WelsTheory/Repositorio-de-Tesis/Demo SAQD_ECG/Tesis_Simulink.X/Tesis_Simulink_data.c

/*
 * -------------------------------------------------------------------
 * MPLAB 16-Bit Device Blocks for Simulink v3.38.
 *
 *   Product Page:  http://www.microchip.com/SimulinkBlocks
 *           Forum: http://www.microchip.com/forums/f192.aspx
 *           Wiki:  http://microchip.wikidot.com/simulink:start
 * -------------------------------------------------------------------
 * File: Tesis_Simulink_data.c
 *
 * Code generated for Simulink model 'Tesis_Simulink'.
 *
 * Model version                  : 1.143
 * Simulink Coder version         : 8.6 (R2014a) 27-Dec-2013
 * C/C++ source code generated on : Sun Jul 07 20:59:31 2019
 */

#include "Tesis_Simulink.h"
#include "Tesis_Simulink_private.h"

/* Constant parameters (auto storage) */
const ConstP_Tesis_Simulink_T Tesis_Simulink_ConstP = {
  /* Computed Parameter: Filtro_40Hz_Orden_20_Coefficients
   * Referenced by: '<S2>/Filtro_40Hz_Orden_20'
   */
  { 0.00203286763F, 0.00379420863F, 0.00820735097F, 0.0163565241F, 0.0286096856F,
    0.0444048606F, 0.0622486696F, 0.0799414217F, 0.0949862376F, 0.105091862F,
    0.108652636F, 0.105091862F, 0.0949862376F, 0.0799414217F, 0.0622486696F,
    0.0444048606F, 0.0286096856F, 0.0163565241F, 0.00820735097F, 0.00379420863F,
    0.00203286763F },

  /* Computed Parameter: Filtro_05Hz_Orden_2_Coefficients
   * Referenced by: '<S2>/Filtro_05Hz_Orden_2'
   */
  { -7.99903137E-5F, -0.00016783434F, -0.000397814467F, -0.000682088779F,
    -0.000912073359F, 0.998920083F, -0.000912073359F, -0.000682088779F,
    -0.000397814467F, -0.00016783434F, -7.99903137E-5F },

  /* Computed Parameter: Filtro_40Hz_Orden_5_Coefficients
   * Referenced by: '<S2>/Filtro_40Hz_Orden_5'
   */
  { 0.0272522252F, 0.141468123F, 0.331279665F, 0.331279665F, 0.141468123F,
    0.0272522252F },

  /* Computed Parameter: Filtro_40Hz_Orden_15_Coefficients
   * Referenced by: '<S2>/Filtro_40Hz_Orden_15'
   */
  { 0.00543942489F, 0.00986033119F, 0.022235956F, 0.0428936221F, 0.0694174543F,
    0.0970705152F, 0.120029137F, 0.133053556F, 0.133053556F, 0.120029137F,
    0.0970705152F, 0.0694174543F, 0.0428936221F, 0.022235956F, 0.00986033119F,
    0.00543942489F },

  /* Computed Parameter: Filtro_40Hz_Orden_30_Coefficients
   * Referenced by: '<S2>/Filtro_40Hz_Orden_30'
   */
  { -0.00108586519F, -0.000820198795F, -0.000399968849F, 0.000607254158F,
    0.00269167544F, 0.00631159171F, 0.011798257F, 0.0192719586F, 0.0285849664F,
    0.0393032022F, 0.0507324189F, 0.0619873591F, 0.072095111F, 0.080117844F,
    0.0852764249F, 0.0870559365F, 0.0852764249F, 0.080117844F, 0.072095111F,
    0.0619873591F, 0.0507324189F, 0.0393032022F, 0.0285849664F, 0.0192719586F,
    0.011798257F, 0.00631159171F, 0.00269167544F, 0.000607254158F,
    -0.000399968849F, -0.000820198795F, -0.00108586519F }
};

/*
 * File trailer for generated code.
 *
 * [EOF]
 */
