WelsTheory/Repositorio-de-Tesis/Demo SAQD_ECG/Tesis_Simulink.X/rt_nonfinite.c

/*
 * -------------------------------------------------------------------
 * MPLAB 16-Bit Device Blocks for Simulink v3.38.
 *
 *   Product Page:  http://www.microchip.com/SimulinkBlocks
 *           Forum: http://www.microchip.com/forums/f192.aspx
 *           Wiki:  http://microchip.wikidot.com/simulink:start
 * -------------------------------------------------------------------
 * File: rt_nonfinite.c
 *
 * Code generated for Simulink model 'Tesis_Simulink'.
 *
 * Model version                  : 1.143
 * Simulink Coder version         : 8.6 (R2014a) 27-Dec-2013
 * C/C++ source code generated on : Sun Jul 07 20:59:31 2019
 */

/*
 * Abstract:
 *      Function to intialize non-finites,
 *      (Inf, NaN and -Inf).
 */
#include "rt_nonfinite.h"
#include "rtGetNaN.h"
#include "rtGetInf.h"

real_T rtInf;
real_T rtMinusInf;
real_T rtNaN;
real32_T rtInfF;
real32_T rtMinusInfF;
real32_T rtNaNF;

/*
 * Initialize the rtInf, rtMinusInf, and rtNaN needed by the
 * generated code. NaN is initialized as non-signaling. Assumes IEEE.
 */
void rt_InitInfAndNaN(size_t realSize)
{
  (void) (realSize);
  rtNaN = rtGetNaN();
  rtNaNF = rtGetNaNF();
  rtInf = rtGetInf();
  rtInfF = rtGetInfF();
  rtMinusInf = rtGetMinusInf();
  rtMinusInfF = rtGetMinusInfF();
}

/* Test if value is infinite */
boolean_T rtIsInf(real_T value)
{
  return (boolean_T)((value==rtInf || value==rtMinusInf) ? 1U : 0U);
}

/* Test if single-precision value is infinite */
boolean_T rtIsInfF(real32_T value)
{
  return (boolean_T)(((value)==rtInfF || (value)==rtMinusInfF) ? 1U : 0U);
}

/* Test if value is not a number */
boolean_T rtIsNaN(real_T value)
{
  return (boolean_T)((value!=value) ? 1U : 0U);
}

/* Test if single-precision value is not a number */
boolean_T rtIsNaNF(real32_T value)
{
  return (boolean_T)(((value!=value) ? 1U : 0U));
}

/*
 * File trailer for generated code.
 *
 * [EOF]
 */
