WelsTheory/Repositorio-de-Tesis/Framework/Ejemplo_de_Programa_principal.X/MCHP_modelInclude.h

/******************************************************/
/* This file includes simulink model public .h files. */
/* File name will not depends on model's name 	      */
/* simplifying inclusion for your shared c/h added    */
/* code (if any)  	                                  */
/******************************************************/

#include "Ejemplo_de_Programa_principal.h"
#include "Ejemplo_de_Programa_principal_private.h"
