WelsTheory/Repositorio-de-Tesis/Carpeta de Pruebas/Prueba_ADC.X/Prueba_ADC_data.c

/*
 * -------------------------------------------------------------------
 * MPLAB 16-Bit Device Blocks for Simulink v3.38.
 *
 *   Product Page:  http://www.microchip.com/SimulinkBlocks
 *           Forum: http://www.microchip.com/forums/f192.aspx
 *           Wiki:  http://microchip.wikidot.com/simulink:start
 * -------------------------------------------------------------------
 * File: Prueba_ADC_data.c
 *
 * Code generated for Simulink model 'Prueba_ADC'.
 *
 * Model version                  : 1.43
 * Simulink Coder version         : 8.6 (R2014a) 27-Dec-2013
 * C/C++ source code generated on : Mon Feb 18 00:49:58 2019
 */

#include "Prueba_ADC.h"
#include "Prueba_ADC_private.h"

/* Constant parameters (auto storage) */
const ConstP_Prueba_ADC_T Prueba_ADC_ConstP = {
  /* Computed Parameter: Filter_0540_HP_1_Coefficients
   * Referenced by: '<Root>/Filter_0540_HP_1'
   */
  { -0.000722855737F, -0.00317084719F, -0.00576246856F, -0.00834118761F,
    -0.0107321292F, -0.0127506247F, -0.0142119713F, -0.01494186F, -0.0147868991F,
    -0.0136246076F, -0.0113722663F, -0.00799405482F, -0.00350597757F,
    0.00202179234F, 0.00846539345F, 0.0156506654F, 0.0233593453F, 0.0313378349F,
    0.0393081084F, 0.0469802357F, 0.0540658571F, 0.0602918938F, 0.0654137582F,
    0.0692273453F, 0.071579136F, 0.0723738372F, 0.071579136F, 0.0692273453F,
    0.0654137582F, 0.0602918938F, 0.0540658571F, 0.0469802357F, 0.0393081084F,
    0.0313378349F, 0.0233593453F, 0.0156506654F, 0.00846539345F, 0.00202179234F,
    -0.00350597757F, -0.00799405482F, -0.0113722663F, -0.0136246076F,
    -0.0147868991F, -0.01494186F, -0.0142119713F, -0.0127506247F, -0.0107321292F,
    -0.00834118761F, -0.00576246856F, -0.00317084719F, -0.000722855737F },

  /* Computed Parameter: Filter_40_HP_50_Coefficients
   * Referenced by: '<Root>/Filter_40_HP_50'
   */
  { -2.66366964E-18F, -0.00287274597F, -0.00591556495F, -0.00894370489F,
    -0.0117507577F, -0.0141187599F, -0.0158297028F, -0.0166778471F,
    -0.0164821465F, -0.0150980344F, -0.012427886F, -0.00842943F, -0.00312157185F,
    0.00341284438F, 0.0110276015F, 0.0195171088F, 0.0286237169F, 0.0380480699F,
    0.0474619828F, 0.0565232038F, 0.0648913532F, 0.0722440779F, 0.0782926604F,
    0.0827961788F, 0.0855734125F, 0.0865118653F, 0.0855734125F, 0.0827961788F,
    0.0782926604F, 0.0722440779F, 0.0648913532F, 0.0565232038F, 0.0474619828F,
    0.0380480699F, 0.0286237169F, 0.0195171088F, 0.0110276015F, 0.00341284438F,
    -0.00312157185F, -0.00842943F, -0.012427886F, -0.0150980344F, -0.0164821465F,
    -0.0166778471F, -0.0158297028F, -0.0141187599F, -0.0117507577F,
    -0.00894370489F, -0.00591556495F, -0.00287274597F, -2.66366964E-18F }
};

/*
 * File trailer for generated code.
 *
 * [EOF]
 */
