WelsTheory/Repositorio-de-Tesis/Carpeta de Pruebas/DSPIC33FJ_FIR.X/DSPIC33FJ_FIR_private.h

/*
 * -------------------------------------------------------------------
 * MPLAB 16-Bit Device Blocks for Simulink v3.38.
 *
 *   Product Page:  http://www.microchip.com/SimulinkBlocks
 *           Forum: http://www.microchip.com/forums/f192.aspx
 *           Wiki:  http://microchip.wikidot.com/simulink:start
 * -------------------------------------------------------------------
 * File: DSPIC33FJ_FIR_private.h
 *
 * Code generated for Simulink model 'DSPIC33FJ_FIR'.
 *
 * Model version                  : 1.77
 * Simulink Coder version         : 8.6 (R2014a) 27-Dec-2013
 * C/C++ source code generated on : Sun Dec 09 18:39:59 2018
 */

#ifndef RTW_HEADER_DSPIC33FJ_FIR_private_h_
#define RTW_HEADER_DSPIC33FJ_FIR_private_h_
#include "rtwtypes.h"
#ifndef __RTWTYPES_H__
#error This file requires rtwtypes.h to be included
#endif                                 /* __RTWTYPES_H__ */

/* Declare UART1 Tx Circular Buffer Structure */
extern MCHP_UART1_TxStr MCHP_UART1_Tx;
extern MCHP_UART1_RxStr MCHP_UART1_Rx;

#endif                                 /* RTW_HEADER_DSPIC33FJ_FIR_private_h_ */

/*
 * File trailer for generated code.
 *
 * [EOF]
 */
