WelsTheory/Repositorio-de-Tesis/Carpeta de Pruebas/ECG_Physionet/Hola/mcode/ADC_DSPIC33.X/rtGetInf.h

/*
 * -------------------------------------------------------------------
 * MPLAB 16-Bit Device Blocks for Simulink v3.38.
 *
 *   Product Page:  http://www.microchip.com/SimulinkBlocks
 *           Forum: http://www.microchip.com/forums/f192.aspx
 *           Wiki:  http://microchip.wikidot.com/simulink:start
 * -------------------------------------------------------------------
 * File: rtGetInf.h
 *
 * Code generated for Simulink model 'ADC_DSPIC33'.
 *
 * Model version                  : 1.216
 * Simulink Coder version         : 8.6 (R2014a) 27-Dec-2013
 * C/C++ source code generated on : Tue Dec 18 17:40:23 2018
 */

#ifndef RTW_HEADER_rtGetInf_h_
#define RTW_HEADER_rtGetInf_h_
#include <stddef.h>
#include "rtwtypes.h"
#include "rt_nonfinite.h"

extern real_T rtGetInf(void);
extern real32_T rtGetInfF(void);
extern real_T rtGetMinusInf(void);
extern real32_T rtGetMinusInfF(void);

#endif                                 /* RTW_HEADER_rtGetInf_h_ */

/*
 * File trailer for generated code.
 *
 * [EOF]
 */
