WelsTheory/Repositorio-de-Tesis/Carpeta de Pruebas/ECG_Physionet/Hola/mcode/Programa_DSPIC.X/rtmodel.h

/*
 * -------------------------------------------------------------------
 * MPLAB 16-Bit Device Blocks for Simulink v3.38.
 *
 *   Product Page:  http://www.microchip.com/SimulinkBlocks
 *           Forum: http://www.microchip.com/forums/f192.aspx
 *           Wiki:  http://microchip.wikidot.com/simulink:start
 * -------------------------------------------------------------------
 * File: rtmodel.h
 *
 * Code generated for Simulink model 'Programa_DSPIC'.
 *
 * Model version                  : 1.9
 * Simulink Coder version         : 8.6 (R2014a) 27-Dec-2013
 * C/C++ source code generated on : Thu Dec 20 15:43:44 2018
 */

#ifndef RTW_HEADER_rtmodel_h_
#define RTW_HEADER_rtmodel_h_
#include "Programa_DSPIC.h"

/* Macros generated for backwards compatibility  */
#ifndef rtmGetErrorStatus
# define rtmGetErrorStatus(rtm)        (NULL)
#endif

#ifndef rtmSetErrorStatus
# define rtmSetErrorStatus(rtm, val)   (NULL)
#endif
#endif                                 /* RTW_HEADER_rtmodel_h_ */

/*
 * File trailer for generated code.
 *
 * [EOF]
 */
