WelsTheory/Repositorio-de-Tesis/Carpeta de Pruebas/hola_dspic.X/hola_dspic_data.c

/*
 * -------------------------------------------------------------------
 * MPLAB 16-Bit Device Blocks for Simulink v3.38.
 *
 *   Product Page:  http://www.microchip.com/SimulinkBlocks
 *           Forum: http://www.microchip.com/forums/f192.aspx
 *           Wiki:  http://microchip.wikidot.com/simulink:start
 * -------------------------------------------------------------------
 * File: hola_dspic_data.c
 *
 * Code generated for Simulink model 'hola_dspic'.
 *
 * Model version                  : 1.124
 * Simulink Coder version         : 8.12 (R2017a) 16-Feb-2017
 * C/C++ source code generated on : Sun Nov 11 19:55:10 2018
 */

#include "hola_dspic.h"
#include "hola_dspic_private.h"

/* Constant parameters (auto storage) */
const ConstP_hola_dspic_T hola_dspic_ConstP = {
  /* Computed Parameter: FIR100_Coefficients
   * Referenced by: '<Root>/FIR100'
   */
  { -2.93238E-18F, -0.00152284489F, -0.00301876059F, -0.00439115381F,
    -0.00554666575F, -0.00640110951F, -0.00688511226F, -0.00694910809F,
    -0.00656735152F, -0.00574067235F, -0.00449775F, -0.00289477361F,
    -0.00101342739F, 0.00104274449F, 0.00315345684F, 0.00518805347F,
    0.00701281102F, 0.00849880371F, 0.00952989142F, 0.010010398F, 0.00987201F,
    0.00907949172F, 0.00763483858F, 0.00557956519F, 0.00299493037F,
    -3.07145458E-18F, -0.00325244456F, -0.00658200914F, -0.00978855882F,
    -0.0126615046F, -0.0149900736F, -0.0165740475F, -0.0172344446F, -0.01682356F,
    -0.0152338631F, -0.0124052288F, -0.00833010115F, -0.00305626774F,
    0.00331296818F, 0.0106212832F, 0.018664442F, 0.0271978304F, 0.0359460711F,
    0.0446143337F, 0.0529007502F, 0.0605094396F, 0.0671634153F, 0.0726168528F,
    0.0766660422F, 0.0791585296F, 0.08F, 0.0791585296F, 0.0766660422F,
    0.0726168528F, 0.0671634153F, 0.0605094396F, 0.0529007502F, 0.0446143337F,
    0.0359460711F, 0.0271978304F, 0.018664442F, 0.0106212832F, 0.00331296818F,
    -0.00305626774F, -0.00833010115F, -0.0124052288F, -0.0152338631F,
    -0.01682356F, -0.0172344446F, -0.0165740475F, -0.0149900736F, -0.0126615046F,
    -0.00978855882F, -0.00658200914F, -0.00325244456F, -3.07145458E-18F,
    0.00299493037F, 0.00557956519F, 0.00763483858F, 0.00907949172F, 0.00987201F,
    0.010010398F, 0.00952989142F, 0.00849880371F, 0.00701281102F, 0.00518805347F,
    0.00315345684F, 0.00104274449F, -0.00101342739F, -0.00289477361F,
    -0.00449775F, -0.00574067235F, -0.00656735152F, -0.00694910809F,
    -0.00688511226F, -0.00640110951F, -0.00554666575F, -0.00439115381F,
    -0.00301876059F, -0.00152284489F, -2.93238E-18F }
};

/*
 * File trailer for generated code.
 *
 * [EOF]
 */
